musitdev/satin_board/software/applications/mpe_cv_converter/src/satinboard.rs

use nb;
use stm32f7;
use stm32f7xx_hal as hal;
//use core::fmt::Write;
//use cortex_m_rt::entry;
use crate::ehal::digital::v2::OutputPin;
use crate::ehal::spi::{Mode, Phase, Polarity};
use crate::hal::{
    dac::{Dac, DacWord, DacWriter},
    //    delay::Delay,
    //    device,
    gpio::*,
    prelude::*,
    serial::{Event, Serial},
    spi,
    spi::{NoMiso, Spi},
    //    timer::{Event as TimerEvent, Timer},
};
use cortex_m::peripheral::DWT;
use cortex_m_semihosting::hprintln;
use nb::block;

//pub const CONST_TIMER_FREQ: u32 = 1;

/// SPI mode
pub const MODE: Mode = Mode {
    phase: Phase::CaptureOnFirstTransition,
    polarity: Polarity::IdleLow,
};

pub struct SatinBoard {
    //      led_discovery: hal::gpio::gpiob::PB7<hal::gpio::Output<hal::gpio::PushPull>>
    pub led1: hal::gpio::gpioh::PH3<hal::gpio::Output<hal::gpio::PushPull>>,
    pub gate_out: hal::gpio::gpioa::PA9<hal::gpio::Output<hal::gpio::PushPull>>,
    pub clock_out: hal::gpio::gpioc::PC6<hal::gpio::Output<hal::gpio::PushPull>>,
    pub note_velocity_dac: Dac,
    pub note_voltage_switch: hal::gpio::gpioa::PA0<hal::gpio::Output<hal::gpio::PushPull>>,
    pub velocity_voltage_switch: hal::gpio::gpioa::PA1<hal::gpio::Output<hal::gpio::PushPull>>,
    pub spi2: Spi<
        stm32f7::stm32f7x6::SPI2,
        (
            gpiod::PD3<Alternate<AF5>>,
            spi::NoMiso,
            gpioi::PI3<Alternate<AF5>>,
        ),
    >,
    pub dac1cv_clear: hal::gpio::gpioi::PI2<hal::gpio::Output<hal::gpio::PushPull>>,

    pub nss_dac1: hal::gpio::gpioa::PA8<hal::gpio::Output<hal::gpio::PushPull>>,
    pub nss_dac2: hal::gpio::gpiod::PD8<hal::gpio::Output<hal::gpio::PushPull>>,
    pub nss_dac3: hal::gpio::gpiod::PD0<hal::gpio::Output<hal::gpio::PushPull>>,
    pub nss_dac4: hal::gpio::gpiod::PD1<hal::gpio::Output<hal::gpio::PushPull>>,
}

impl SatinBoard {
    pub fn output_note(&mut self, note: u8, velocity: u8) {
        if velocity == 0 {
            self.output_note_off();
        } else {
            let cv_note = crate::satinapi::cv::convert_note_to_cv(note, 0);
            //hprintln!("no:{:?} cv:{:?} v:{}", note, cv_note, velocity).unwrap();
            //enable gate out
            self.gate_out.set_high();
            //for test set dac1 level depend on the note. TODO convertion table.
            //note
            self.note_velocity_dac
                .dac1()
                .write(DacWord::B8_ALIGN_R(cv_note));
            //Velocity
            self.note_velocity_dac
                .dac2()
                .write(DacWord::B8_ALIGN_R(velocity * 2));
        }
    }
    pub fn output_note_off(&mut self) {
        //disable gate out
        self.gate_out.set_low();
    }

    pub fn write_sp2_cv1(&mut self, data: u16) -> Result<(), nb::Error<stm32f7xx_hal::spi::Error>> {
        //use dac1 nns to low to selec the dac.
        //        self.dac1cv_clear.set_low();
        //        self.dac1cv_clear.set_high();
        write_spi2(data, &mut self.spi2, &mut self.nss_dac1)?;
        Ok(())
    }
    pub fn write_sp2_cv2(&mut self, data: u16) -> Result<(), nb::Error<stm32f7xx_hal::spi::Error>> {
        //use dac1 nns to low to selec the dac.
        //        self.dac1cv_clear.set_low();
        //        self.dac1cv_clear.set_high();
        write_spi2(data, &mut self.spi2, &mut self.nss_dac2)?;
        Ok(())
    }
    pub fn write_sp2_cv3(&mut self, data: u16) -> Result<(), nb::Error<stm32f7xx_hal::spi::Error>> {
        //use dac1 nns to low to selec the dac.
        //        self.dac1cv_clear.set_low();
        //        self.dac1cv_clear.set_high();
        write_spi2(data, &mut self.spi2, &mut self.nss_dac3)?;
        Ok(())
    }
    pub fn write_sp2_cv4(&mut self, data: u16) -> Result<(), nb::Error<stm32f7xx_hal::spi::Error>> {
        //use dac1 nns to low to selec the dac.
        //        self.dac1cv_clear.set_low();
        //        self.dac1cv_clear.set_high();
        write_spi2(data, &mut self.spi2, &mut self.nss_dac4)?;
        Ok(())
    }
}

fn write_spi2<PIN>(
    data: u16,
    spi2: &mut Spi<
        stm32f7::stm32f7x6::SPI2,
        (
            gpiod::PD3<Alternate<AF5>>,
            spi::NoMiso,
            gpioi::PI3<Alternate<AF5>>,
        ),
    >,
    nss: &mut PIN,
) -> Result<(), nb::Error<stm32f7xx_hal::spi::Error>>
where
    PIN: OutputPin,
{
    let valeur_dac: u16 = 0x3FFF & data; //clear control bit D15, D14
    let valeur_dac: u16 = 0x4000 | valeur_dac; //set controle bit D14 up

    nss.set_low()
        .unwrap_or_else(|_| hprintln!("write_spi2 nss set low error.").unwrap());
    if let Err(err) = block!(spi2.send_only_16b(valeur_dac)) {
        return Err(nb::Error::Other(err));
    }
    /*    if let Err(err) = spi2.read() {
        //read one time at the end to end the transation and way the end of the send
        match err {
            nb::Error::WouldBlock => (), //do  nothing
            _ => return Err(nb::Error::Other(spi::Error::EndTranscationReadError)),
        }
    }
    if let Err(err) = spi2.read() {
        //read one time at the end to end the transation and way the end of the send
        match err {
            nb::Error::WouldBlock => (), //do  nothing
            _ => return Err(nb::Error::Other(spi::Error::EndTranscationReadError)),
        }
    } */
    nss.set_high()
        .unwrap_or_else(|_| hprintln!("write_spi2 nss set high error.").unwrap());

    Ok(())
}

pub fn init_board(
    device: stm32f7::stm32f7x6::Peripherals,
) -> (
    stm32f7xx_hal::serial::Tx<stm32f7::stm32f7x6::USART2>,
    stm32f7xx_hal::serial::Rx<stm32f7::stm32f7x6::USART2>,
    //    Timer<stm32f7::stm32f7x6::TIM2>,
    SatinBoard,
) {
    let rcc = device.RCC.constrain();
    let clocks = rcc.cfgr.sysclk(216.mhz()).freeze();

    unsafe { (*DWT::ptr()).lar.write(0xC5ACCE55) };

    //        let clocks = rcc.cfgr.sysclk(180.mhz()).freeze();
    //    let mut systick = Timer::tim2(device.TIM2, CONST_TIMER_FREQ.hz(), clocks, &mut rcc.apb1);
    //    systick.listen(TimerEvent::TimeOut);

    //serial init
    let gpioa = device.GPIOA.split();
    let gpiob = device.GPIOB.split();
    let gpioc = device.GPIOC.split();
    let gpiod = device.GPIOD.split();

    let tx = gpiod.pd5.into_alternate_af7();
    let rx = gpiod.pd6.into_alternate_af7();
    //        let mut serial = Serial::usart2(device.USART2, (tx, rx), 115_200.bps(), clocks, false);
    let mut serial = Serial::usart2(device.USART2, (tx, rx), 31_250.bps(), clocks, true);

    //        serial.listen(Event::Txe);
    serial.listen(Event::Rxne);

    let (tx, rx) = serial.split();

    //Dac and SPI GPIO init

    let gpiog = device.GPIOG.split();
    let gpioh = device.GPIOH.split();
    let gpioi = device.GPIOI.split();

    //init led 1 to high
    let mut led1: hal::gpio::gpioh::PH3<hal::gpio::Output<hal::gpio::PushPull>> =
        gpioh.ph3.into_push_pull_output();
    led1.set_high()
        .unwrap_or_else(|_| hprintln!("init_board led1 set high error.").unwrap());

    //init STM32 dac
    //SWITCH_NOTE 0-10V / -5,5V: PA0
    let mut note_voltage_switch: hal::gpio::gpioa::PA0<hal::gpio::Output<hal::gpio::PushPull>> =
        gpioa.pa0.into_push_pull_output();
    note_voltage_switch
        .set_low()
        .unwrap_or_else(|_| hprintln!("init_board note_voltage_switch set low error.").unwrap());

    //  SWITCH_VELOCITE 0-10V / -5,5V: PA1
    let mut velocity_voltage_switch: hal::gpio::gpioa::PA1<hal::gpio::Output<hal::gpio::PushPull>> =
        gpioa.pa1.into_push_pull_output();
    velocity_voltage_switch.set_low().unwrap_or_else(|_| {
        hprintln!("init_board velocity_voltage_switch set low error.").unwrap()
    });

    //Dac1 pin CV Note: ST_DAC_OUT1 PA4
    let dac1_pin = gpioa.pa4.into_analog_output();
    //Dac2 pin CV vélocity: ST_DAC_OUT2: PA5
    let dac2_pin = gpioa.pa5.into_analog_output();

    let dac = Dac::new(device.DAC);
    let mut dac1 = dac.create_dac_channel1(dac1_pin);
    dac1.enable();
    dac1.disable_output_buffer();
    dac1.disable_trigger();

    let mut dac2 = dac.create_dac_channel2(dac2_pin);
    dac2.enable();
    dac2.disable_output_buffer();
    dac2.disable_trigger();

    //test write
    dac1.write(DacWord::B8_ALIGN_R(0));
    dac2.write(DacWord::B8_ALIGN_R(0));

    hprintln!("end dac init").unwrap();

    //Configure Gate / Clock
    //clock out PC6
    let mut clock_out: hal::gpio::gpioc::PC6<hal::gpio::Output<hal::gpio::PushPull>> =
        gpioc.pc6.into_push_pull_output();
    clock_out
        .set_low()
        .unwrap_or_else(|_| hprintln!("init_board clock_out set low error.").unwrap());

    // gate out PA9
    let mut gate_out: hal::gpio::gpioa::PA9<hal::gpio::Output<hal::gpio::PushPull>> =
        gpioa.pa9.into_push_pull_output();
    gate_out
        .set_high()
        .unwrap_or_else(|_| hprintln!("init_board gate_out set_high error.").unwrap());

    //Gate PA9 + invertion gate: PI8
    let mut invertion_gate: hal::gpio::gpioi::PI8<hal::gpio::Output<hal::gpio::PushPull>> =
        gpioi.pi8.into_push_pull_output();
    invertion_gate
        .set_low()
        .unwrap_or_else(|_| hprintln!("init_board invertion_gate set low error.").unwrap());

    //clock out PC6 INVERSION_CLOCK PI9
    let mut invertion_clock: hal::gpio::gpioi::PI9<hal::gpio::Output<hal::gpio::PushPull>> =
        gpioi.pi9.into_push_pull_output();
    invertion_clock
        .set_low()
        .unwrap_or_else(|_| hprintln!("init_board invertion_clock set low error.").unwrap());

    //4 SPI CV dac.
    //Dac1 CS PA8
    let mut nss_dac1 = gpioa.pa8.into_push_pull_output();
    nss_dac1
        .set_high()
        .unwrap_or_else(|_| hprintln!("init_board nss_dac1 set_high error.").unwrap()); //no data

    //Dac2 CS PD8
    let mut nss_dac2 = gpiod.pd8.into_push_pull_output();
    nss_dac2
        .set_high()
        .unwrap_or_else(|_| hprintln!("init_board nss_dac2 set_high error.").unwrap()); //no data

    //DAC3_CS PD0
    let mut nss_dac3 = gpiod.pd0.into_push_pull_output();
    nss_dac3
        .set_high()
        .unwrap_or_else(|_| hprintln!("init_board nss_dac3 set_high error.").unwrap()); //no data

    //DAC4_CS PD1
    let mut nss_dac4 = gpiod.pd1.into_push_pull_output();
    nss_dac4
        .set_high()
        .unwrap_or_else(|_| hprintln!("init_board nss_dac4 set_high error.").unwrap()); //no data

    //Dac1, Dac2, Dac 3 Dac 4 are controled via SPI2
    //SPI2:
    /*SPI2 GPIO Configuration
    PD3     ------> SPI2_SCK
    pas de SPI2 MISO.
    PI3     ------> SPI2_MOSI
    */
    let sck = gpiod.pd3.into_alternate_af5();
    let miso = NoMiso;
    let mosi = gpioi.pi3.into_alternate_af5();

    let spi2 = Spi::spi2(
        device.SPI2,
        (sck, miso, mosi),
        MODE,
        // 1.mhz(),
        100.khz().into(),
        clocks,
    );

    //DAC-CV clear init PI2
    let mut dac1cv_clear: hal::gpio::gpioi::PI2<hal::gpio::Output<hal::gpio::PushPull>> =
        gpioi.pi2.into_push_pull_output();
    dac1cv_clear
        .set_high()
        .unwrap_or_else(|_| hprintln!("init_board dac1cv_clear set_high error.").unwrap());

    //DAC-CV CV3:

    //SWITCH_CV_n1 switch 0-10 / -5,5v  PB14
    let mut cv3_voltage_switch: hal::gpio::gpiob::PB14<hal::gpio::Output<hal::gpio::PushPull>> =
        gpiob.pb14.into_push_pull_output();
    cv3_voltage_switch
        .set_high()
        .unwrap_or_else(|_| hprintln!("init_board cv3_voltage_switch set_high error.").unwrap());

    //SWITCH_CVn2_OUTSwitch 0-5v ou (0-10 / -5,5v)  PB11
    let mut cv3_end_voltage_switch: hal::gpio::gpiob::PB11<hal::gpio::Output<hal::gpio::PushPull>> =
        gpiob.pb11.into_push_pull_output();
    cv3_end_voltage_switch.set_high().unwrap_or_else(|_| {
        hprintln!("init_board cv3_end_voltage_switch set_high error.").unwrap()
    });

    //SWITCH_CV_n3 switch 0-10 / -5,5v  PH12
    let mut cv4_voltage_switch: hal::gpio::gpioh::PH12<hal::gpio::Output<hal::gpio::PushPull>> =
        gpioh.ph12.into_push_pull_output();
    cv4_voltage_switch
        .set_low()
        .unwrap_or_else(|_| hprintln!("init_board cv4_voltage_switch set_low error.").unwrap());

    //SWITCH_CVn4_OUTSwitch 0-5v ou (0-10 / -5,5v)  PB12
    let mut cv4_end_voltage_switch: hal::gpio::gpiob::PB12<hal::gpio::Output<hal::gpio::PushPull>> =
        gpiob.pb12.into_push_pull_output();
    cv4_end_voltage_switch
        .set_low()
        .unwrap_or_else(|_| hprintln!("init_board cv4_end_voltage_switch set_low error.").unwrap());

    //switch CV(5-6) out or  stéreo DAC:   SWITCH_CV_STEREO OUT: PG2
    let mut cv_st_out_switch = gpiog.pg2.into_push_pull_output();
    cv_st_out_switch
        .set_low()
        .unwrap_or_else(|_| hprintln!("init_board cv_st_out_switch set_low error.").unwrap()); //no data

    let board = SatinBoard {
        //      led_discovery: hal::gpio::gpiob::PB7<hal::gpio::Output<hal::gpio::PushPull>>
        led1: led1,
        gate_out,
        clock_out,
        note_velocity_dac: dac,
        note_voltage_switch,
        velocity_voltage_switch,
        spi2,
        dac1cv_clear,
        nss_dac1,
        nss_dac2,
        nss_dac3,
        nss_dac4,
    };
    hprintln!("end board init").unwrap();

    (tx, rx, board)
}
